Mehmet-Emre-Dogan/wirelessMusicVisualizer/neoVuTransmitter/dialog13.h

// Created by http://oleddisplay.squix.ch/ Consider a donation
// In case of problems make sure that you are using the font file with the correct version!
const uint8_t Dialog_plain_13Bitmaps[] PROGMEM = {

	// Bitmap Data:
	0x00, // ' '
	0xAA,0xA2,0x80, // '!'
	0xAA,0xAA, // '"'
	0x09,0x04,0x81,0x21,0xFE,0x12,0x09,0x0F,0xF0,0x90,0x24,0x1A,0x00, // '#'
	0x10,0x7C,0x92,0x90,0x70,0x1E,0x12,0x92,0x7C,0x10,0x10, // '$'
	0x60,0x89,0x10,0x92,0x09,0x20,0x64,0xC0,0x92,0x09,0x21,0x12,0x20,0xC0, // '%'
	0x38,0x11,0x04,0x00,0x80,0x50,0xA2,0x28,0x53,0x0C,0x7C,0x80, // '&'
	0xAA, // '''
	0x64,0x48,0x88,0x88,0x84,0x42, // '('
	0x84,0x42,0x22,0x22,0x24,0x48, // ')'
	0x10,0x92,0x7C,0x38,0xD6,0x10, // '*'
	0x08,0x02,0x00,0x80,0x20,0xFF,0x82,0x00,0x80,0x20,0x08,0x00, // '+'
	0x4A,0x00, // ','
	0xE0, // '-'
	0xA0, // '.'
	0x10,0x88,0x42,0x31,0x08,0x44,0x20, // '/'
	0x78,0x92,0x14,0x28,0x50,0xA1,0x24,0x78, // '0'
	0xE0,0x82,0x08,0x20,0x82,0x08,0xF8, // '1'
	0x79,0x18,0x10,0x20,0x82,0x08,0x20,0xFC, // '2'
	0x79,0x08,0x10,0x23,0x80,0x81,0x42,0x78, // '3'
	0x18,0x50,0xA2,0x44,0x91,0x3F,0x04,0x08, // '4'
	0xF9,0x02,0x07,0xC0,0xC0,0x81,0x46,0x78, // '5'
	0x38,0x8A,0x05,0xCC,0xD0,0xA1,0x26,0x78, // '6'
	0xFC,0x08,0x20,0x41,0x02,0x08,0x10,0x40, // '7'
	0x79,0x0A,0x14,0x27,0x90,0xA1,0x42,0x78, // '8'
	0x79,0x92,0x14,0x2C,0xCE,0x81,0x44,0x70, // '9'
	0xA0,0x28, // ':'
	0x48,0x00,0x94, // ';'
	0x01,0x07,0x1C,0x10,0x07,0x00,0x70,0x04, // '<'
	0xFF,0x00,0x00,0x1F,0xE0, // '='
	0x80,0x38,0x03,0x80,0x20,0xE3,0x82,0x00, // '>'
	0x72,0x20,0x84,0x20,0x80,0x08,0x20, // '?'
	0x1F,0x02,0x0C,0x40,0x48,0xF2,0x91,0x29,0x12,0x91,0x48,0xF8,0x40,0x02,0x08,0x1F,0x00, // '@'
	0x08,0x05,0x01,0x40,0x88,0x22,0x1F,0xC4,0x11,0x04,0x80,0x80, // 'A'
	0xFC,0x82,0x82,0x82,0xFC,0x82,0x82,0x82,0xFC, // 'B'
	0x3C,0x42,0x80,0x80,0x80,0x80,0x80,0x42,0x3C, // 'C'
	0xFC,0x43,0x20,0x50,0x28,0x14,0x0A,0x05,0x0C,0xFC,0x00, // 'D'
	0xFD,0x02,0x04,0x0F,0xD0,0x20,0x40,0xFC, // 'E'
	0xFA,0x08,0x20,0xFA,0x08,0x20,0x80, // 'F'
	0x3E,0x20,0xA0,0x10,0x08,0x74,0x0A,0x04,0x82,0x3E,0x00, // 'G'
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
};
const GFXglyph Dialog_plain_13Glyphs[] PROGMEM = {
// bitmapOffset, width, height, xAdvance, xOffset, yOffset
	  {     0,   1,   1,   5,    0,    0 }, // ' '
	  {     1,   2,   9,   6,    2,   -9 }, // '!'
	  {     4,   4,   4,   6,    1,   -9 }, // '"'
	  {     6,  10,  10,  12,    1,  -10 }, // '#'
	  {    19,   8,  11,   9,    1,   -9 }, // '$'
	  {    30,  12,   9,  13,    0,   -9 }, // '%'
	  {    44,  10,   9,  12,    1,   -9 }, // '&'
	  {    56,   2,   4,   4,    1,   -9 }, // '''
	  {    57,   4,  12,   6,    1,  -11 }, // '('
	  {    63,   4,  12,   6,    1,  -11 }, // ')'
	  {    69,   8,   6,   8,    0,   -9 }, // '*'
	  {    75,  10,   9,  12,    1,   -9 }, // '+'
	  {    87,   3,   3,   5,    1,   -2 }, // ','
	  {    89,   4,   1,   6,    1,   -4 }, // '-'
	  {    90,   2,   2,   5,    2,   -2 }, // '.'
	  {    91,   5,  11,   5,    0,   -9 }, // '/'
	  {    98,   7,   9,   9,    1,   -9 }, // '0'
	  {   106,   6,   9,   9,    2,   -9 }, // '1'
	  {   113,   7,   9,   9,    1,   -9 }, // '2'
	  {   121,   7,   9,   9,    1,   -9 }, // '3'
	  {   129,   7,   9,   9,    1,   -9 }, // '4'
	  {   137,   7,   9,   9,    1,   -9 }, // '5'
	  {   145,   7,   9,   9,    1,   -9 }, // '6'
	  {   153,   7,   9,   9,    1,   -9 }, // '7'
	  {   161,   7,   9,   9,    1,   -9 }, // '8'
	  {   169,   7,   9,   9,    1,   -9 }, // '9'
	  {   177,   2,   7,   5,    2,   -7 }, // ':'
	  {   179,   3,   8,   5,    1,   -7 }, // ';'
	  {   182,   9,   7,  12,    1,   -8 }, // '<'
	  {   190,   9,   4,  12,    1,   -6 }, // '='
	  {   195,   9,   7,  12,    1,   -8 }, // '>'
	  {   203,   6,   9,   8,    1,   -9 }, // '?'
	  {   210,  12,  11,  14,    1,   -9 }, // '@'
	  {   227,  10,   9,  10,    0,   -9 }, // 'A'
	  {   239,   8,   9,  10,    1,   -9 }, // 'B'
	  {   248,   8,   9,  10,    1,   -9 }, // 'C'
	  {   257,   9,   9,  11,    1,   -9 }, // 'D'
	  {   268,   7,   9,   9,    1,   -9 }, // 'E'
	  {   276,   6,   9,   8,    1,   -9 }, // 'F'
	  {   283,   9,   9,  11,    1,   -9 }, // 'G'
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
};
const GFXfont Dialog_plain_13 PROGMEM = {
(uint8_t  *)Dialog_plain_13Bitmaps,(GFXglyph *)Dialog_plain_13Glyphs,0x20, 0x7E, 17};
