Mehmet-Emre-Dogan/wirelessMusicVisualizer/neoVuTransmitter/dialog11.h

// Created by http://oleddisplay.squix.ch/ Consider a donation
// In case of problems make sure that you are using the font file with the correct version!
const uint8_t Dialog_plain_11Bitmaps[] PROGMEM = {

	// Bitmap Data:
	0x00, // ' '
	0xAA,0xA2, // '!'
	0xAA,0xA0, // '"'
	0x12,0x0A,0x1F,0xC4,0x82,0x47,0xF0,0xA0,0x90, // '#'
	0x21,0xEA,0x28,0x70,0xA2,0xBC,0x20,0x80, // '$'
	0x62,0x25,0x09,0x41,0xA0,0x0B,0x05,0x21,0x48,0x8C, // '%'
	0x30,0x24,0x10,0x0C,0x09,0x14,0x53,0x10,0xF6, // '&'
	0xA8, // '''
	0x52,0x49,0x24,0x88, // '('
	0x91,0x24,0x92,0x90, // ')'
	0x22,0xA7,0x1C,0xA8,0x80, // '*'
	0x10,0x10,0x10,0xFE,0x10,0x10,0x10, // '+'
	0xA0, // ','
	0xE0, // '-'
	0x80, // '.'
	0x11,0x88,0x46,0x21,0x18,0x80, // '/'
	0x73,0x68,0xA2,0x8A,0x2D,0x9C, // '0'
	0xE0,0x82,0x08,0x20,0x82,0x3E, // '1'
	0x72,0x20,0x82,0x10,0x84,0x3E, // '2'
	0x72,0x20,0x9C,0x08,0x28,0x9C, // '3'
	0x08,0x30,0xA2,0x48,0x9F,0x82,0x04, // '4'
	0xF2,0x08,0x3C,0x08,0x20,0xBC, // '5'
	0x39,0x08,0x3C,0x8A,0x28,0x9C, // '6'
	0xF8,0x21,0x04,0x20,0x82,0x10, // '7'
	0x72,0x28,0x9C,0x8A,0x28,0x9C, // '8'
	0x72,0x28,0xA2,0x78,0x21,0x38, // '9'
	0x80,0x20, // ':'
	0x80,0x28, // ';'
	0x02,0x1C,0xE0,0xE0,0x1C,0x02, // '<'
	0xFE,0x00,0xFE, // '='
	0x80,0x70,0x0E,0x0E,0x70,0x80, // '>'
	0xE0,0x8C,0xC4,0x20,0x08, // '?'
	0x1F,0x0C,0x31,0x01,0x47,0x29,0x25,0x25,0xA3,0xC2,0x00,0x61,0x03,0xC0, // '@'
	0x10,0x28,0x28,0x28,0x44,0x7C,0x44,0x82, // 'A'
	0xF9,0x0A,0x17,0xC8,0x50,0xA1,0x7C, // 'B'
	0x38,0x8A,0x04,0x08,0x10,0x11,0x1C, // 'C'
	0xF1,0x12,0x14,0x28,0x50,0xA2,0x78, // 'D'
	0xFA,0x08,0x3E,0x82,0x08,0x3E, // 'E'
	0xFA,0x08,0x3E,0x82,0x08,0x20, // 'F'
	0x3C,0x42,0x80,0x80,0x8E,0x82,0x42,0x3C, // 'G'
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
};
const GFXglyph Dialog_plain_11Glyphs[] PROGMEM = {
// bitmapOffset, width, height, xAdvance, xOffset, yOffset
	  {     0,   1,   1,   5,    0,    0 }, // ' '
	  {     1,   2,   8,   4,    1,   -8 }, // '!'
	  {     3,   4,   3,   6,    1,   -8 }, // '"'
	  {     5,   9,   8,  10,    1,   -8 }, // '#'
	  {    14,   6,  10,   8,    1,   -8 }, // '$'
	  {    22,  10,   8,  11,    0,   -8 }, // '%'
	  {    32,   9,   8,  11,    1,   -8 }, // '&'
	  {    41,   2,   3,   4,    1,   -8 }, // '''
	  {    42,   3,  10,   5,    1,   -9 }, // '('
	  {    46,   3,  10,   5,    1,   -9 }, // ')'
	  {    50,   6,   6,   7,    0,   -8 }, // '*'
	  {    55,   8,   7,  10,    1,   -7 }, // '+'
	  {    62,   2,   2,   5,    1,   -1 }, // ','
	  {    63,   4,   1,   5,    1,   -4 }, // '-'
	  {    64,   2,   1,   5,    1,   -1 }, // '.'
	  {    65,   5,   9,   5,    0,   -8 }, // '/'
	  {    71,   6,   8,   8,    1,   -8 }, // '0'
	  {    77,   6,   8,   8,    1,   -8 }, // '1'
	  {    83,   6,   8,   8,    1,   -8 }, // '2'
	  {    89,   6,   8,   8,    1,   -8 }, // '3'
	  {    95,   7,   8,   8,    0,   -8 }, // '4'
	  {   102,   6,   8,   8,    1,   -8 }, // '5'
	  {   108,   6,   8,   8,    1,   -8 }, // '6'
	  {   114,   6,   8,   8,    1,   -8 }, // '7'
	  {   120,   6,   8,   8,    1,   -8 }, // '8'
	  {   126,   6,   8,   8,    1,   -8 }, // '9'
	  {   132,   2,   6,   5,    1,   -6 }, // ':'
	  {   134,   2,   7,   5,    1,   -6 }, // ';'
	  {   136,   8,   6,  10,    1,   -6 }, // '<'
	  {   142,   8,   3,  10,    1,   -5 }, // '='
	  {   145,   8,   6,  10,    1,   -6 }, // '>'
	  {   151,   5,   8,   7,    1,   -8 }, // '?'
	  {   156,  11,  10,  13,    1,   -8 }, // '@'
	  {   170,   8,   8,   8,    0,   -8 }, // 'A'
	  {   178,   7,   8,   9,    1,   -8 }, // 'B'
	  {   185,   7,   8,   9,    1,   -8 }, // 'C'
	  {   192,   7,   8,   9,    1,   -8 }, // 'D'
	  {   199,   6,   8,   8,    1,   -8 }, // 'E'
	  {   205,   6,   8,   7,    1,   -8 }, // 'F'
	  {   211,   8,   8,  10,    1,   -8 }, // 'G'
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
};
const GFXfont Dialog_plain_11 PROGMEM = {
(uint8_t  *)Dialog_plain_11Bitmaps,(GFXglyph *)Dialog_plain_11Glyphs,0x20, 0x7E, 14};
