Mehmet-Emre-Dogan/wirelessMusicVisualizer/neoVuTransmitter/dialog7.h

// Created by http://oleddisplay.squix.ch/ Consider a donation
// In case of problems make sure that you are using the font file with the correct version!
const uint8_t Dialog_plain_7Bitmaps[] PROGMEM = {

	// Bitmap Data:
	0x00, // ' '
	0xA8,0x80, // '!'
	0xAA, // '"'
	0x53,0xE5,0x3E,0x60, // '#'
	0x4E,0xCE,0x6E,0x40, // '$'
	0xC9,0xA3,0xF1,0x64,0xC0, // '%'
	0x71,0x0E,0xAC,0x78, // '&'
	0xA0, // '''
	0x52,0x48,0x80, // '('
	0x89,0x25,0x00, // ')'
	0x4E,0x4E, // '*'
	0x20,0x8F,0x88,0x20, // '+'
	0xA0, // ','
	0xC0, // '-'
	0x80, // '.'
	0x49,0x49,0x00, // '/'
	0xEA,0xAA,0xE0, // '0'
	0xC4,0x44,0xE0, // '1'
	0xE2,0x24,0xE0, // '2'
	0xE2,0x42,0xE0, // '3'
	0x23,0x19,0xE2,0x00, // '4'
	0xE8,0xE2,0xE0, // '5'
	0x68,0xEA,0xE0, // '6'
	0xE2,0x24,0x40, // '7'
	0xEA,0x4A,0xE0, // '8'
	0xEA,0xE2,0xC0, // '9'
	0x82, // ':'
	0x82,0x80, // ';'
	0x17,0x38,0x20, // '<'
	0xF0,0x3C, // '='
	0x83,0x9D,0x00, // '>'
	0xE2,0x40,0x40, // '?'
	0x79,0x8A,0xD5,0xCC,0x0E,0x00, // '@'
	0x21,0xC5,0x1C,0x88, // 'A'
	0xF4,0xB9,0x2F,0x00, // 'B'
	0x74,0x21,0x07,0x00, // 'C'
	0xE4,0xA5,0x2E,0x00, // 'D'
	0xE8,0xE8,0xE0, // 'E'
	0xE8,0xE8,0x80, // 'F'
	0x74,0x2D,0x27,0x00, // 'G'
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
};
const GFXglyph Dialog_plain_7Glyphs[] PROGMEM = {
// bitmapOffset, width, height, xAdvance, xOffset, yOffset
	  {     0,   1,   1,   3,    0,    0 }, // ' '
	  {     1,   2,   5,   4,    1,   -5 }, // '!'
	  {     3,   4,   2,   4,    1,   -5 }, // '"'
	  {     4,   6,   5,   7,    1,   -5 }, // '#'
	  {     8,   4,   7,   5,    1,   -6 }, // '$'
	  {    12,   7,   5,   8,    1,   -5 }, // '%'
	  {    17,   6,   5,   6,    1,   -5 }, // '&'
	  {    21,   2,   2,   3,    1,   -5 }, // '''
	  {    22,   3,   6,   4,    1,   -6 }, // '('
	  {    25,   3,   6,   4,    1,   -6 }, // ')'
	  {    28,   4,   4,   5,    1,   -5 }, // '*'
	  {    30,   6,   5,   7,    1,   -5 }, // '+'
	  {    34,   2,   2,   3,    1,   -1 }, // ','
	  {    35,   3,   1,   4,    1,   -3 }, // '-'
	  {    36,   2,   1,   3,    1,   -1 }, // '.'
	  {    37,   3,   6,   3,    0,   -5 }, // '/'
	  {    40,   4,   5,   5,    1,   -5 }, // '0'
	  {    43,   4,   5,   5,    1,   -5 }, // '1'
	  {    46,   4,   5,   5,    1,   -5 }, // '2'
	  {    49,   4,   5,   5,    1,   -5 }, // '3'
	  {    52,   5,   5,   5,    1,   -5 }, // '4'
	  {    56,   4,   5,   5,    1,   -5 }, // '5'
	  {    59,   4,   5,   5,    1,   -5 }, // '6'
	  {    62,   4,   5,   5,    1,   -5 }, // '7'
	  {    65,   4,   5,   5,    1,   -5 }, // '8'
	  {    68,   4,   5,   5,    1,   -5 }, // '9'
	  {    71,   2,   4,   3,    1,   -4 }, // ':'
	  {    72,   2,   5,   3,    1,   -4 }, // ';'
	  {    74,   5,   4,   7,    1,   -4 }, // '<'
	  {    77,   5,   3,   7,    1,   -4 }, // '='
	  {    79,   5,   4,   7,    1,   -4 }, // '>'
	  {    82,   4,   5,   5,    1,   -5 }, // '?'
	  {    85,   7,   6,   8,    1,   -5 }, // '@'
	  {    91,   6,   5,   6,    0,   -5 }, // 'A'
	  {    95,   5,   5,   6,    1,   -5 }, // 'B'
	  {    99,   5,   5,   6,    1,   -5 }, // 'C'
	  {   103,   5,   5,   6,    1,   -5 }, // 'D'
	  {   107,   4,   5,   5,    1,   -5 }, // 'E'
	  {   110,   4,   5,   5,    1,   -5 }, // 'F'
	  {   113,   5,   5,   6,    1,   -5 }, // 'G'
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
};
const GFXfont Dialog_plain_7 PROGMEM = {
(uint8_t  *)Dialog_plain_7Bitmaps,(GFXglyph *)Dialog_plain_7Glyphs,0x20, 0x7E, 9};
