Mehmet-Emre-Dogan/wirelessMusicVisualizer/neoVuTransmitter/dialog9.h

// Created by http://oleddisplay.squix.ch/ Consider a donation
// In case of problems make sure that you are using the font file with the correct version!
const uint8_t Dialog_plain_9Bitmaps[] PROGMEM = {

	// Bitmap Data:
	0x00, // ' '
	0xAA,0x88, // '!'
	0xAA, // '"'
	0x28,0x53,0xF1,0x4F,0xCA,0x14,0x00, // '#'
	0x21,0xEA,0x38,0x38,0xAF,0x08, // '$'
	0xE4,0x52,0x2A,0x1F,0xE1,0x51,0x28,0x9C, // '%'
	0x30,0x91,0x03,0x29,0x53,0x1B,0x00, // '&'
	0xA0, // '''
	0x52,0x49,0x22, // '('
	0x91,0x24,0xA4, // ')'
	0xA9,0xC7,0x2A, // '*'
	0x20,0x8F,0x88,0x20, // '+'
	0xA0, // ','
	0xC0, // '-'
	0x80, // '.'
	0x22,0x44,0x48,0x80, // '/'
	0x64,0xA5,0x29,0x49,0x80, // '0'
	0xC4,0x44,0x44,0xE0, // '1'
	0x64,0x84,0x44,0x43,0xC0, // '2'
	0x64,0x84,0xC1,0x0B,0x80, // '3'
	0x10,0xC5,0x14,0x93,0xE1,0x00, // '4'
	0xF4,0x21,0xC1,0x0B,0x80, // '5'
	0x76,0x21,0xC9,0x49,0x80, // '6'
	0xF0,0x88,0x42,0x21,0x00, // '7'
	0x64,0xA4,0xC9,0x49,0x80, // '8'
	0x64,0xA5,0xE1,0x1B,0x80, // '9'
	0x80,0x80, // ':'
	0x80,0xA0, // ';'
	0x04,0x73,0x01,0xC0,0x40, // '<'
	0xFC,0x03,0xF0, // '='
	0x80,0xE0,0x33,0x88,0x00, // '>'
	0xF0,0x88,0x84,0x01,0x00, // '?'
	0x3C,0x21,0x27,0x54,0xAA,0x54,0xF1,0x10,0x70, // '@'
	0x30,0x61,0x22,0x47,0x90,0xA1,0x00, // 'A'
	0xF2,0x28,0xBC,0x8A,0x2F,0x00, // 'B'
	0x73,0x28,0x20,0x83,0x07,0x80, // 'C'
	0xF2,0x68,0xA2,0x8A,0x6F,0x00, // 'D'
	0xF4,0x21,0xE8,0x43,0xC0, // 'E'
	0xF4,0x21,0xE8,0x42,0x00, // 'F'
	0x73,0x28,0x26,0x8B,0x27,0x00, // 'G'
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
};
const GFXglyph Dialog_plain_9Glyphs[] PROGMEM = {
// bitmapOffset, width, height, xAdvance, xOffset, yOffset
	  {     0,   1,   1,   4,    0,    0 }, // ' '
	  {     1,   2,   7,   4,    1,   -7 }, // '!'
	  {     3,   4,   2,   5,    1,   -7 }, // '"'
	  {     4,   7,   7,   9,    1,   -7 }, // '#'
	  {    11,   6,   8,   7,    0,   -7 }, // '$'
	  {    17,   9,   7,  10,    0,   -7 }, // '%'
	  {    25,   7,   7,   9,    1,   -7 }, // '&'
	  {    32,   2,   2,   3,    1,   -7 }, // '''
	  {    33,   3,   8,   5,    1,   -8 }, // '('
	  {    36,   3,   8,   5,    1,   -8 }, // ')'
	  {    39,   6,   4,   6,    0,   -7 }, // '*'
	  {    42,   6,   5,   9,    1,   -5 }, // '+'
	  {    46,   2,   2,   4,    1,   -1 }, // ','
	  {    47,   3,   1,   4,    1,   -3 }, // '-'
	  {    48,   2,   1,   4,    1,   -1 }, // '.'
	  {    49,   4,   7,   4,    0,   -7 }, // '/'
	  {    53,   5,   7,   7,    1,   -7 }, // '0'
	  {    58,   4,   7,   7,    2,   -7 }, // '1'
	  {    62,   5,   7,   7,    1,   -7 }, // '2'
	  {    67,   5,   7,   7,    1,   -7 }, // '3'
	  {    72,   6,   7,   7,    1,   -7 }, // '4'
	  {    78,   5,   7,   7,    1,   -7 }, // '5'
	  {    83,   5,   7,   7,    1,   -7 }, // '6'
	  {    88,   5,   7,   7,    1,   -7 }, // '7'
	  {    93,   5,   7,   7,    1,   -7 }, // '8'
	  {    98,   5,   7,   7,    1,   -7 }, // '9'
	  {   103,   2,   5,   4,    1,   -5 }, // ':'
	  {   105,   2,   6,   4,    1,   -5 }, // ';'
	  {   107,   7,   5,   9,    1,   -5 }, // '<'
	  {   112,   7,   3,   9,    1,   -4 }, // '='
	  {   115,   7,   5,   9,    1,   -5 }, // '>'
	  {   120,   5,   7,   6,    1,   -7 }, // '?'
	  {   125,   9,   8,  11,    1,   -7 }, // '@'
	  {   134,   7,   7,   7,    0,   -7 }, // 'A'
	  {   141,   6,   7,   8,    1,   -7 }, // 'B'
	  {   147,   6,   7,   8,    1,   -7 }, // 'C'
	  {   153,   6,   7,   8,    1,   -7 }, // 'D'
	  {   159,   5,   7,   7,    1,   -7 }, // 'E'
	  {   164,   5,   7,   7,    1,   -7 }, // 'F'
	  {   169,   6,   7,   8,    1,   -7 }, // 'G'
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
};
const GFXfont Dialog_plain_9 PROGMEM = {
(uint8_t  *)Dialog_plain_9Bitmaps,(GFXglyph *)Dialog_plain_9Glyphs,0x20, 0x7E, 12};
